dot1nt/OpenLap/src/rx5808.h

#pragma once

#include <stdint.h>

class Rx5808 {
 public:
  Rx5808(uint8_t inputPin, uint8_t selPin);
  void init();
  void setFrequency(uint16_t freq);
  int readRssi();

 private:
  uint8_t m_selPin;    // CS (CH2)
  uint8_t m_inputPin;  // RSSI
};
